lxsang/Rpi-LPC1114FN28-interface/schematic/images/schematic.min.png

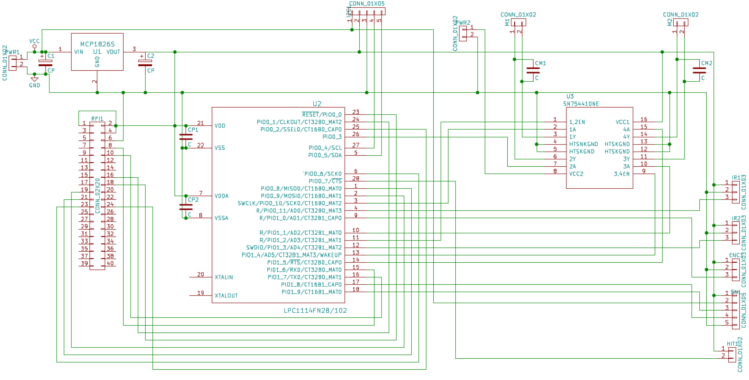
schematic/images/schematic.min.png
